PhilippSchulzGit/GLaDOS_Temporary/CAD/GLaDOS from Instructable/Moving GlaDOS lamp/GlaDOS Head V1.1.STL

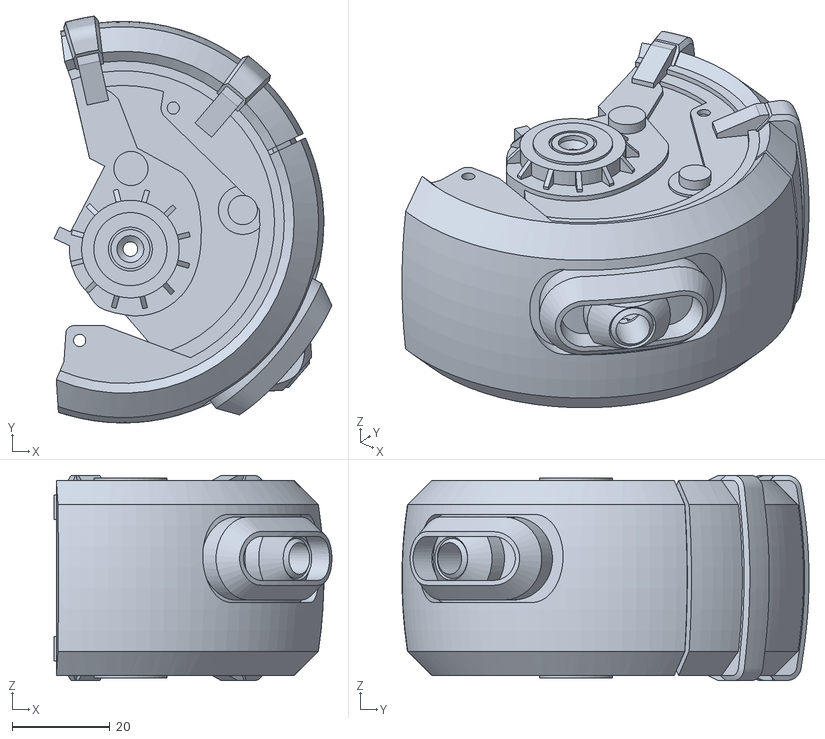
[picture p17: CAD file, 2021-06-26]
CAD/GLaDOS from Instructable/Moving GlaDOS lamp/GlaDOS Head V1.1.STL
56.9 x 83.3 x 42.0
