PhilippSchulzGit/GLaDOS_Temporary/CAD/GLaDOS from Instructable/Stationary GlaDOS lamp/Stationary GlaDOS moving arm V1.1.STL

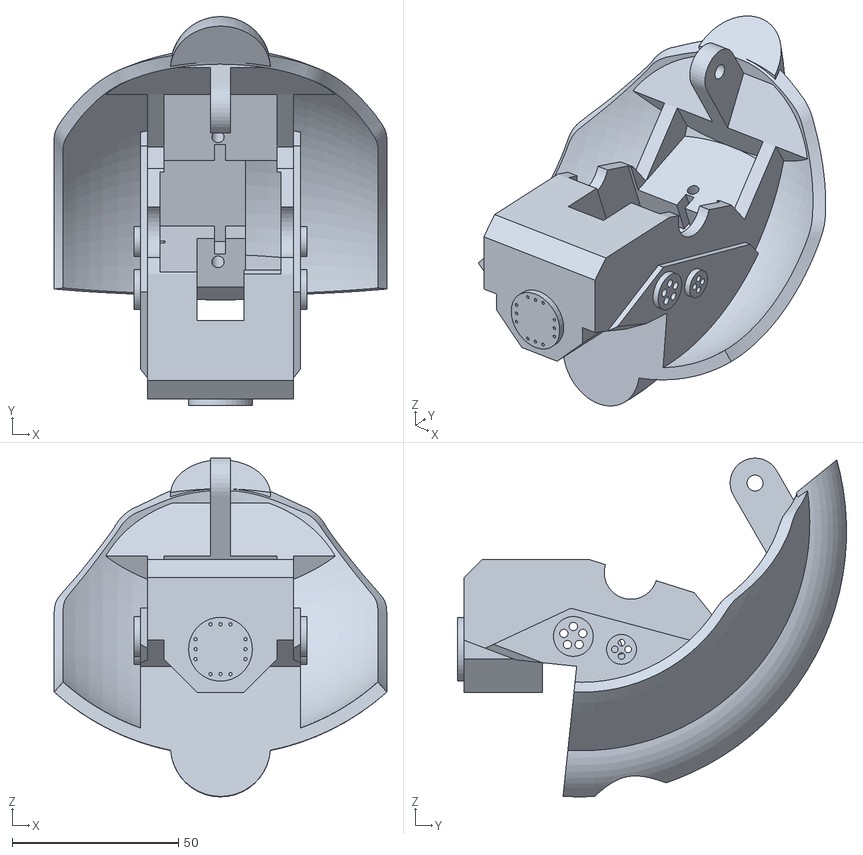
[picture p18: CAD file, 2021-06-26]
CAD/GLaDOS from Instructable/Stationary GlaDOS lamp/Stationary GlaDOS moving arm V1.1.STL
100.0 x 117.0 x 101.9
