PhilippSchulzGit/GLaDOS_Temporary/CAD/Stamps for red spots on GLaDOS/Stempel rote spots 3 (gespiegelt).FCStd

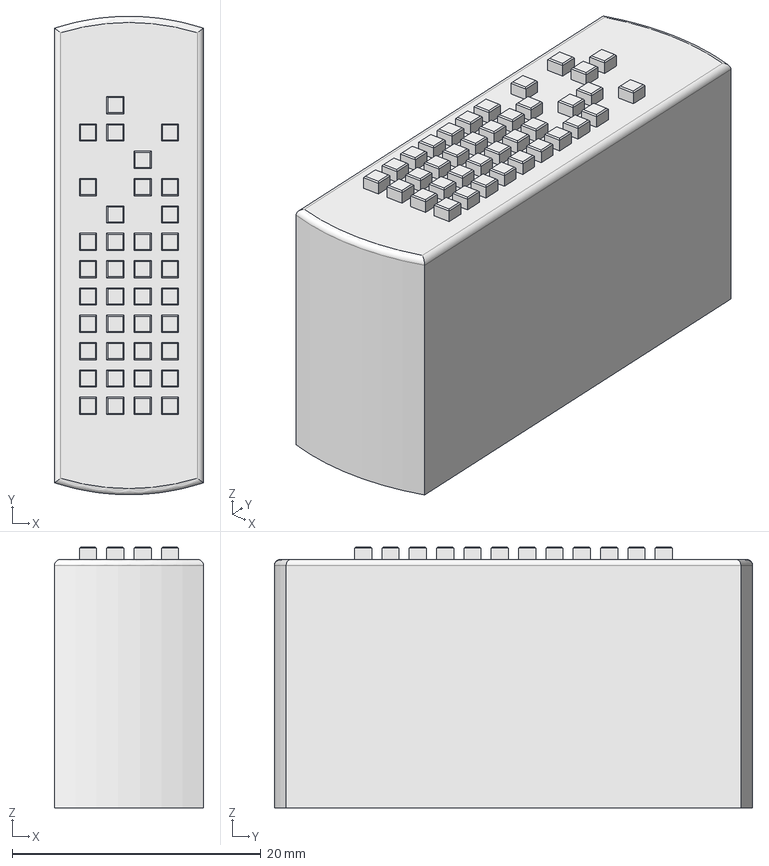
[picture p19: CAD file, 2021-06-26]
CAD/Stamps for red spots on GLaDOS/Stempel rote spots 3 (gespiegelt).FCStd
12.0 x 38.5 x 21.0 mm
