PhilippSchulzGit/GLaDOS_Temporary/CAD/GLaDOS from Instructable/Moving GlaDOS lamp/GlaDOS Servoclamp.STL

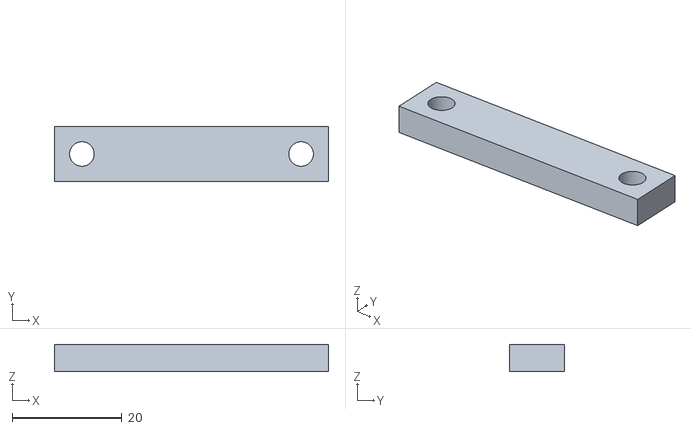
[picture p20: CAD file, 2021-06-26]
CAD/GLaDOS from Instructable/Moving GlaDOS lamp/GlaDOS Servoclamp.STL
50.0 x 10.0 x 5.00
