PhilippSchulzGit/GLaDOS_Temporary/CAD/GLaDOS from Instructable/Stationary GlaDOS lamp/GlaDOS Rotation V1.1.STL

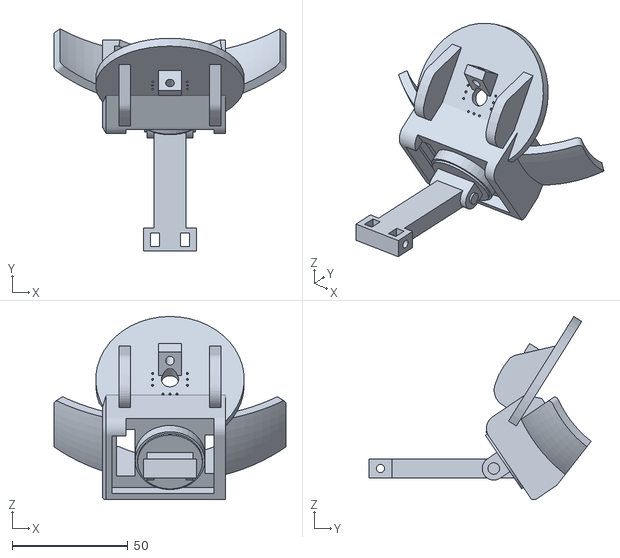
[picture p21: CAD file, 2021-06-26]
CAD/GLaDOS from Instructable/Stationary GlaDOS lamp/GlaDOS Rotation V1.1.STL
100.0 x 95.8 x 78.9
