PhilippSchulzGit/GLaDOS_Temporary/CAD/GLaDOS from Instructable/Moving GlaDOS lamp/GlaDOS Base Ring Fan in.STL

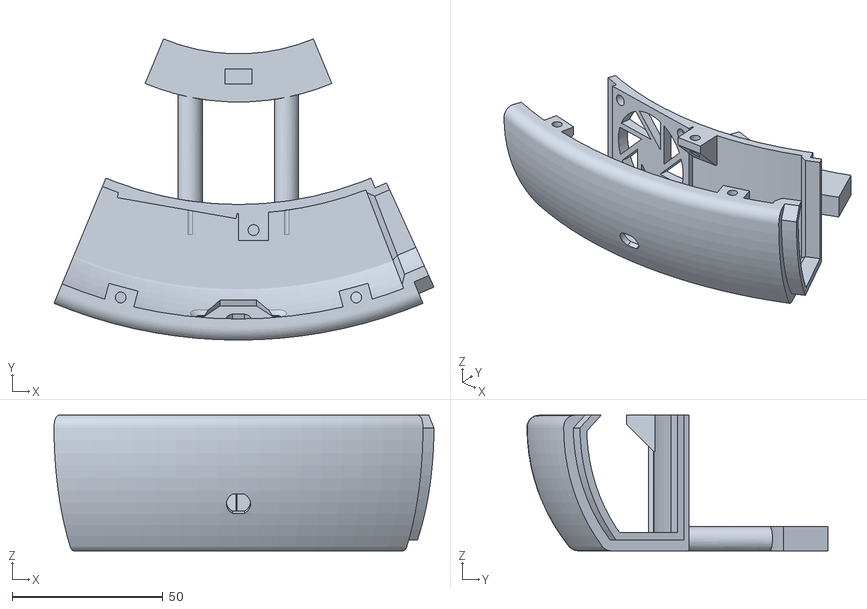
[picture p22: CAD file, 2021-06-26]
CAD/GLaDOS from Instructable/Moving GlaDOS lamp/GlaDOS Base Ring Fan in.STL
126.1 x 99.9 x 45.0
