PhilippSchulzGit/GLaDOS_Temporary/CAD/GLaDOS from Instructable/Moving GlaDOS lamp/GlaDOS Wireblock Large 2.STL

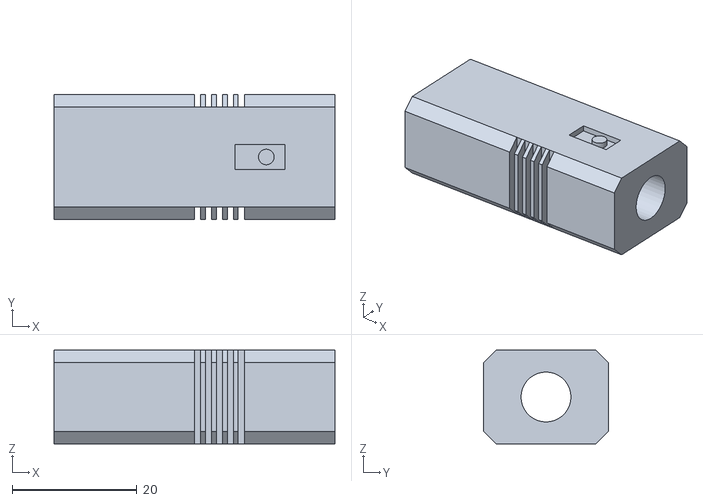
[picture p23: CAD file, 2021-06-26]
CAD/GLaDOS from Instructable/Moving GlaDOS lamp/GlaDOS Wireblock Large 2.STL
45.0 x 20.0 x 15.0
