PhilippSchulzGit/GLaDOS_Temporary/CAD/GLaDOS from Instructable/Moving GlaDOS lamp/Pushrod head.STL

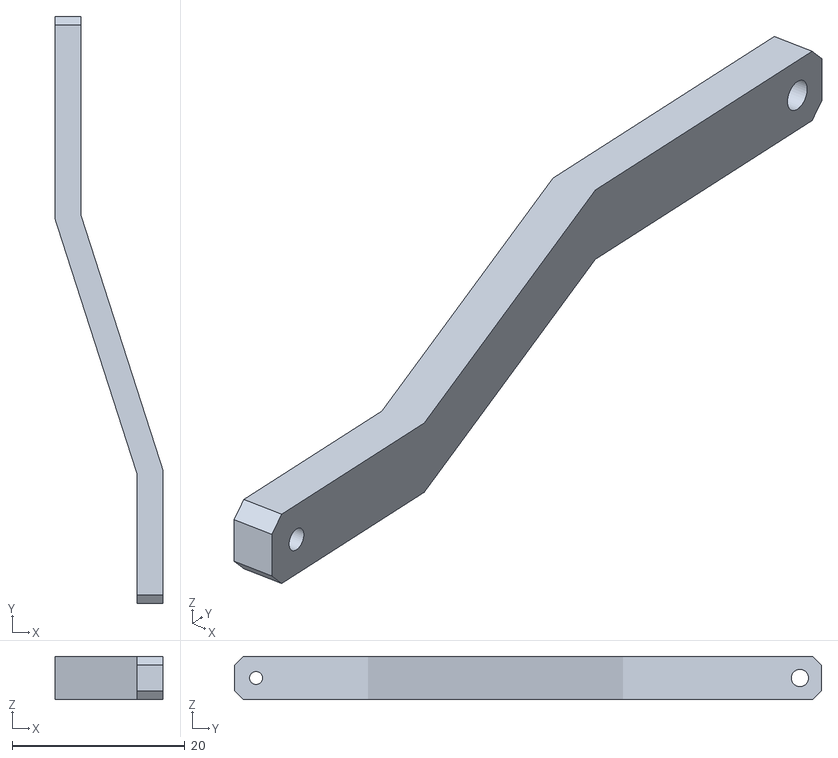
[picture p24: CAD file, 2021-06-26]
CAD/GLaDOS from Instructable/Moving GlaDOS lamp/Pushrod head.STL
12.5 x 68.0 x 5.00
