PhilippSchulzGit/GLaDOS_Temporary/CAD/GLaDOS from Instructable/Stationary GlaDOS lamp/Stationary GlaDOS Base.STL

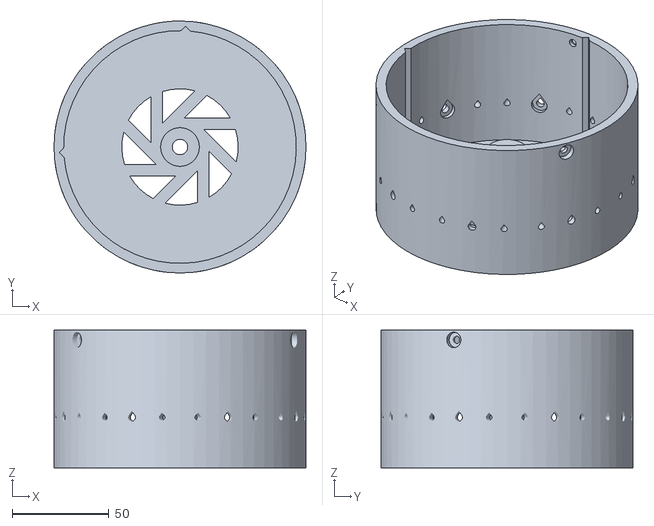
[picture p25: CAD file, 2021-06-26]
CAD/GLaDOS from Instructable/Stationary GlaDOS lamp/Stationary GlaDOS Base.STL
130.0 x 130.0 x 71.0
