PhilippSchulzGit/GLaDOS_Temporary/CAD/GLaDOS from Instructable/Stationary GlaDOS lamp/Stationary GlaDOS Servoclamp.STL

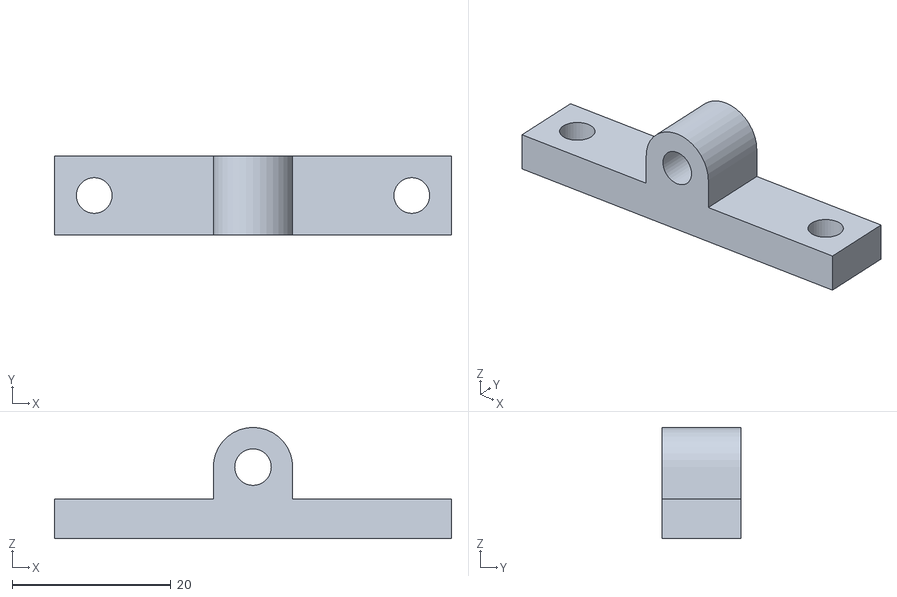
[picture p26: CAD file, 2021-06-26]
CAD/GLaDOS from Instructable/Stationary GlaDOS lamp/Stationary GlaDOS Servoclamp.STL
50.0 x 10.0 x 14.0
