PhilippSchulzGit/GLaDOS_Temporary/CAD/GLaDOS from Instructable/Moving GlaDOS lamp/GlaDOS Base Ring Fan out.STL

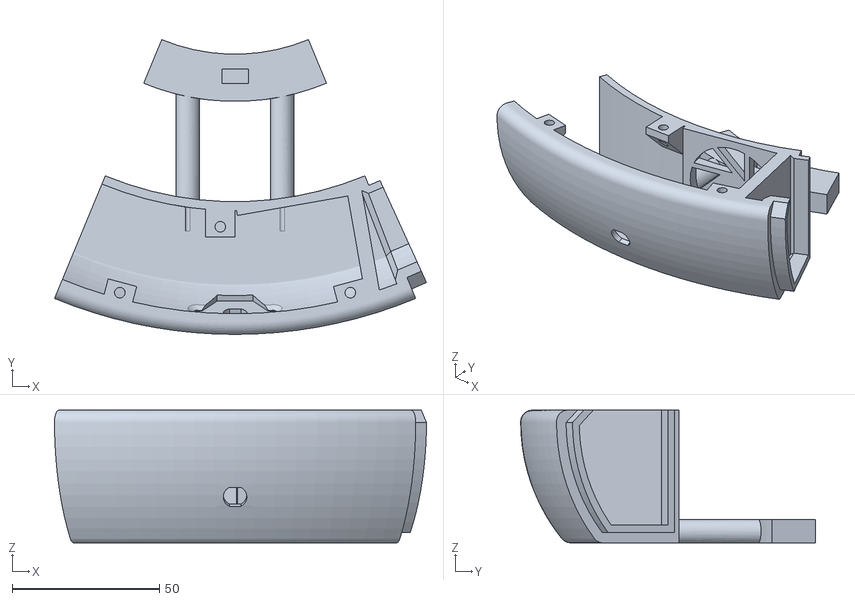
[picture p27: CAD file, 2021-06-26]
CAD/GLaDOS from Instructable/Moving GlaDOS lamp/GlaDOS Base Ring Fan out.STL
126.1 x 99.9 x 45.0
