PhilippSchulzGit/GLaDOS_Temporary/CAD/GLaDOS from Instructable/Stationary GlaDOS lamp/Stationary Glados Pushrod large.STL

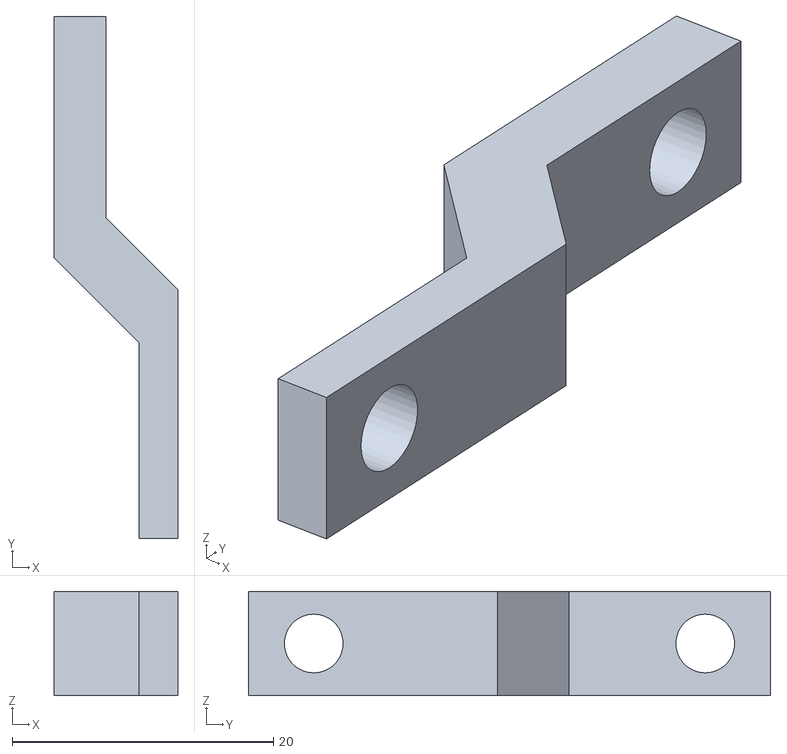
[picture p28: CAD file, 2021-06-26]
CAD/GLaDOS from Instructable/Stationary GlaDOS lamp/Stationary Glados Pushrod large.STL
9.50 x 40.0 x 8.00
