PhilippSchulzGit/GLaDOS_Temporary/CAD/GLaDOS from Instructable/Moving GlaDOS lamp/GlaDOS Rotation Juction box V1.1.STL

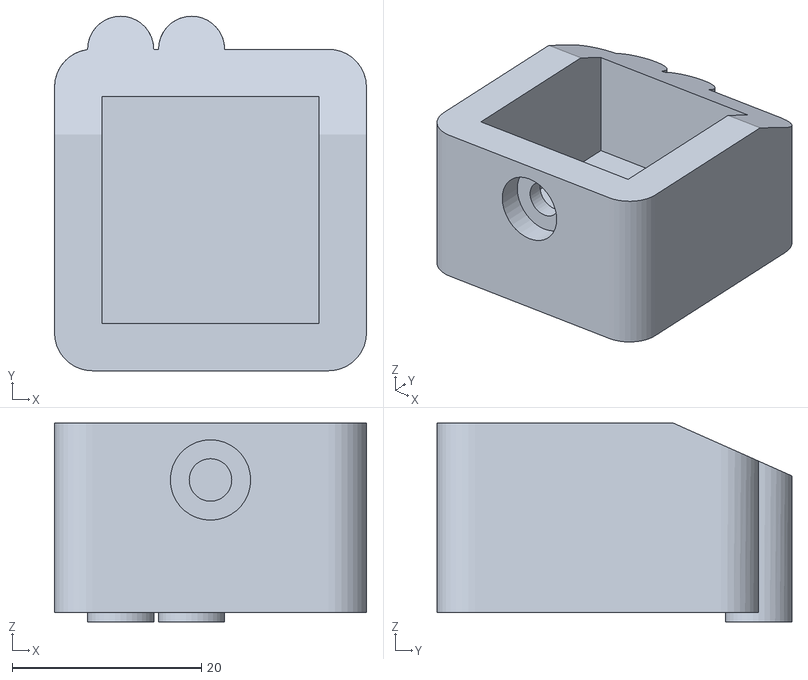
[picture p29: CAD file, 2021-06-26]
CAD/GLaDOS from Instructable/Moving GlaDOS lamp/GlaDOS Rotation Juction box V1.1.STL
33.0 x 37.5 x 21.0
