PhilippSchulzGit/GLaDOS_Temporary/CAD/GLaDOS from Instructable/Stationary GlaDOS lamp/GlaDOS Wireblock Top right.STL

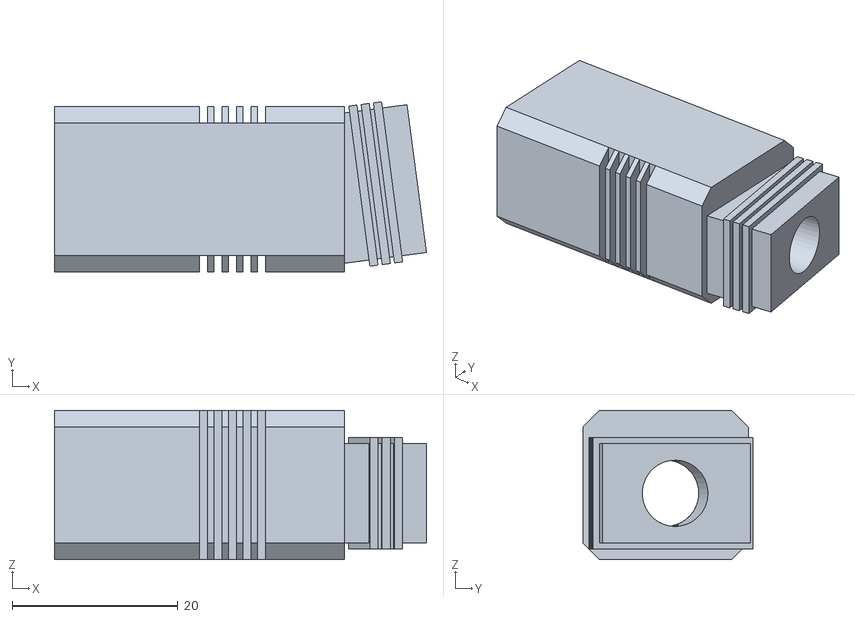
[picture p30: CAD file, 2021-06-26]
CAD/GLaDOS from Instructable/Stationary GlaDOS lamp/GlaDOS Wireblock Top right.STL
44.9 x 20.6 x 18.0
