PhilippSchulzGit/GLaDOS_Temporary/CAD/GLaDOS from Instructable/Stationary GlaDOS lamp/GlaDOS Wireblock Top left.STL

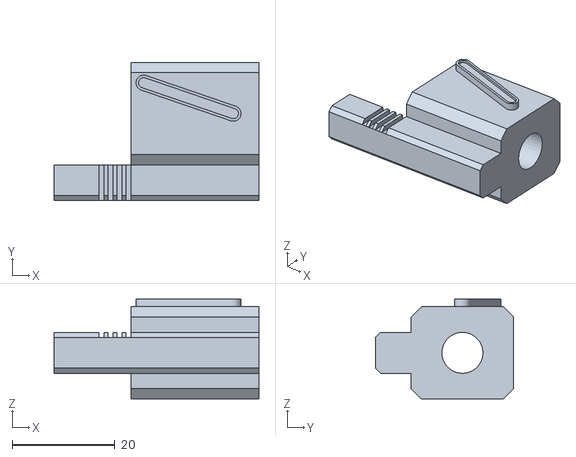
[picture p31: CAD file, 2021-06-26]
CAD/GLaDOS from Instructable/Stationary GlaDOS lamp/GlaDOS Wireblock Top left.STL
40.0 x 27.0 x 19.5
