PhilippSchulzGit/GLaDOS_Temporary/CAD/GLaDOS from Instructable/Stationary GlaDOS lamp/GlaDOS Wireblock small 2.STL

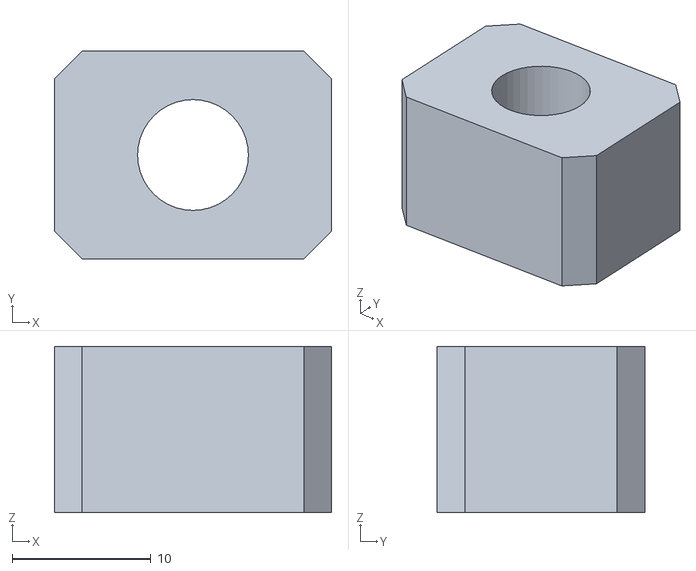
[picture p33: CAD file, 2021-06-26]
CAD/GLaDOS from Instructable/Stationary GlaDOS lamp/GlaDOS Wireblock small 2.STL
20.0 x 15.0 x 12.0
