PhilippSchulzGit/GLaDOS_Temporary/CAD/GLaDOS from Instructable/Moving GlaDOS lamp/GlaDOS Gearbrace V1.1.STL

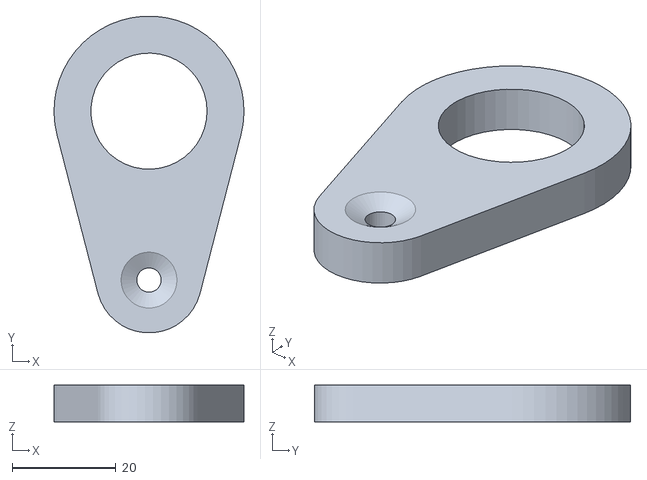
[picture p34: CAD file, 2021-06-26]
CAD/GLaDOS from Instructable/Moving GlaDOS lamp/GlaDOS Gearbrace V1.1.STL
36.7 x 61.1 x 7.14
