PhilippSchulzGit/GLaDOS_Temporary/CAD/GLaDOS from Instructable/Moving GlaDOS lamp/Glados Mounting plate wires.stl

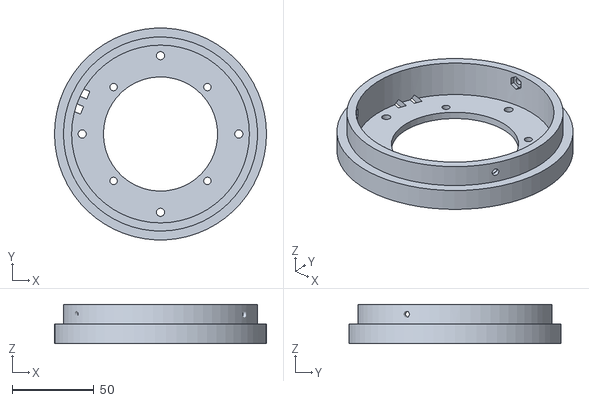
[picture p36: CAD file, 2021-06-26]
CAD/GLaDOS from Instructable/Moving GlaDOS lamp/Glados Mounting plate wires.stl
130.0 x 129.8 x 24.0
