PhilippSchulzGit/GLaDOS_Temporary/CAD/GLaDOS from Instructable/Moving GlaDOS lamp/Glados Pushrod large.STL

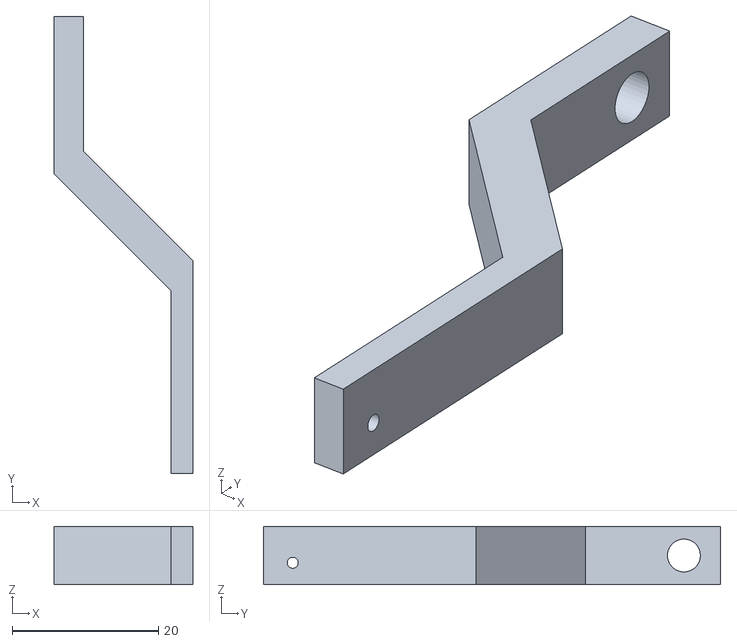
[picture p37: CAD file, 2021-06-26]
CAD/GLaDOS from Instructable/Moving GlaDOS lamp/Glados Pushrod large.STL
19.0 x 62.5 x 8.00
