PhilippSchulzGit/GLaDOS_Temporary/CAD/GLaDOS from Instructable/Moving GlaDOS lamp/SPUR gear 2M 16T driver.STL

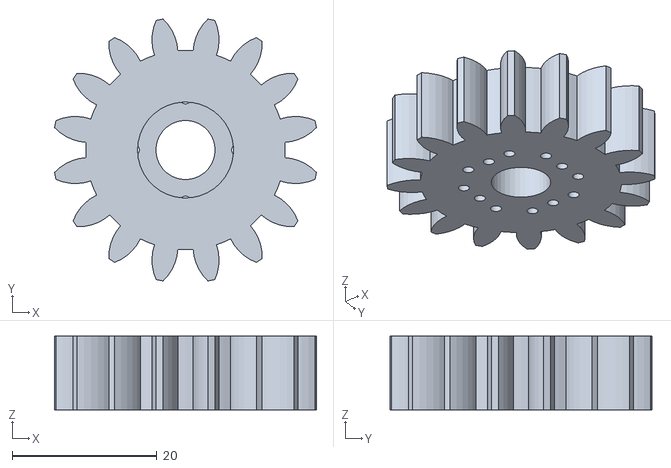
[picture p38: CAD file, 2021-06-26]
CAD/GLaDOS from Instructable/Moving GlaDOS lamp/SPUR gear 2M 16T driver.STL
36.2 x 36.2 x 10.2
